AREM-Projets/Robot-CdR-2025/Docs/Architecture ancienne du robot/Images/STM32_actionneur.webp

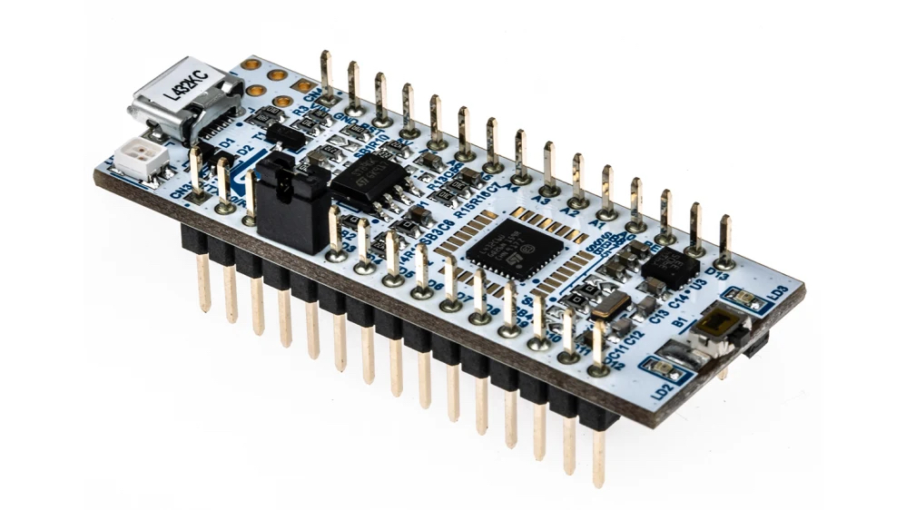
Docs/Architecture ancienne du robot/Images/STM32_actionneur.webp
