AREM-Projets/Robot-CdR-2025/Docs/Architecture ancienne du robot/Images/STM32_embase.jpg

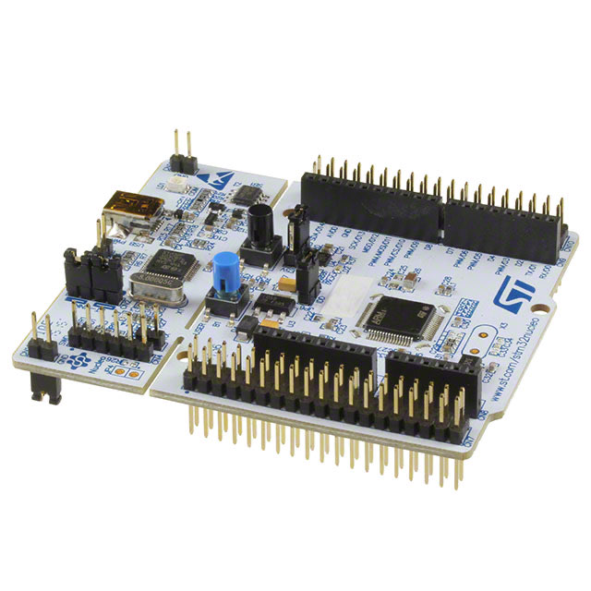
Docs/Architecture ancienne du robot/Images/STM32_embase.jpg
