AREM-Projets/Robot-CdR-2025/Docs/Architecture ancienne du robot/Images/TOF.jpg

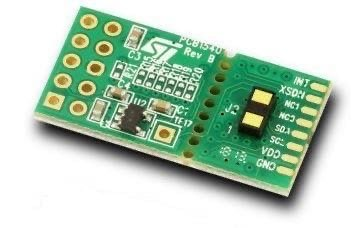
Docs/Architecture ancienne du robot/Images/TOF.jpg
