AREM-Projets/Robot-CdR-2025/Docs/Architecture ancienne du robot/Rendus/Architecture_hardware&electroniquePuissance.png

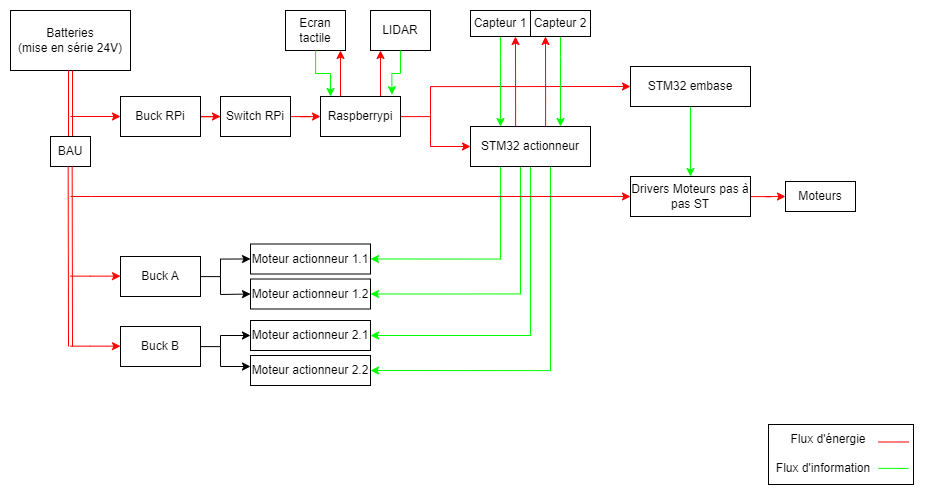
Docs/Architecture ancienne du robot/Rendus/Architecture_hardware&electroniquePuissance.png
