AREM-Projets/Robot-CdR-2025/Docs/Architecture nouvelle du robot/Diagramme_robot_CdR2025.drawio.png

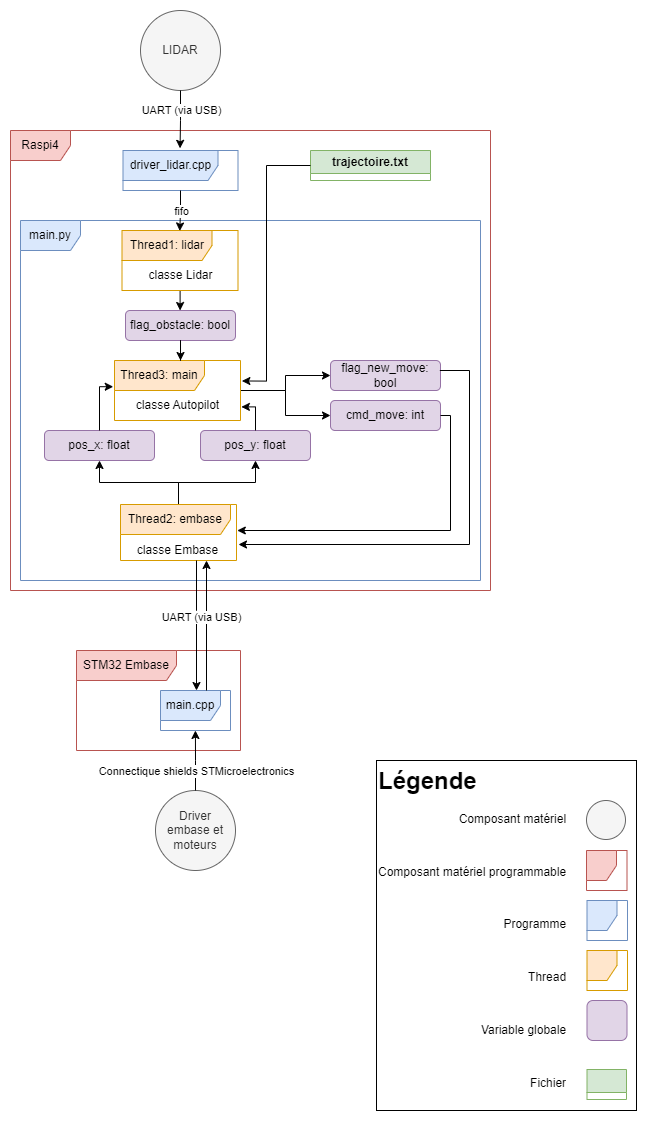
Docs/Architecture nouvelle du robot/Diagramme_robot_CdR2025.drawio.png
